seanperkins/ashleys-bed/output/media/ashleys-bed-closed.png

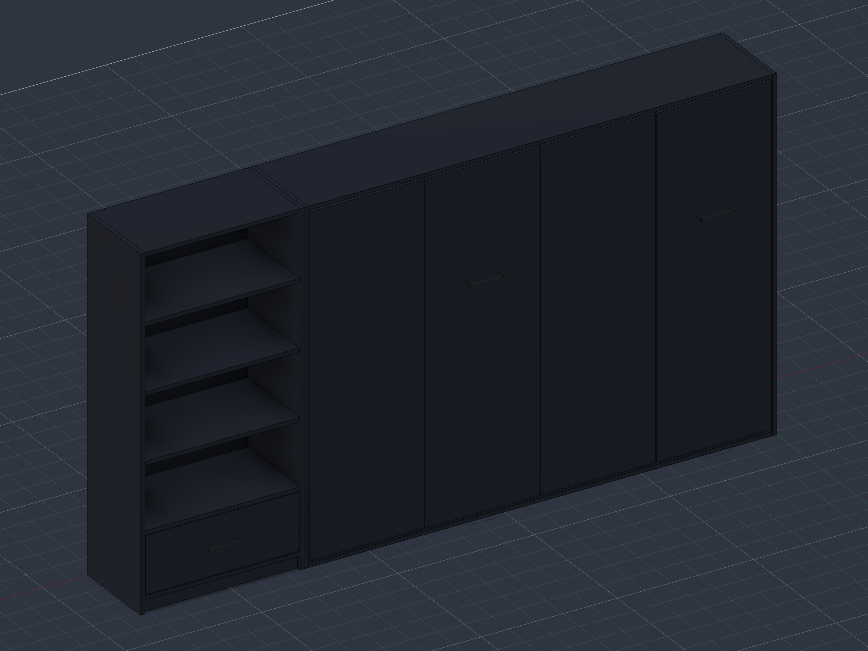
output/media/ashleys-bed-closed.png
