seanperkins/ashleys-bed/output/media/ashleys-bed-frame.png

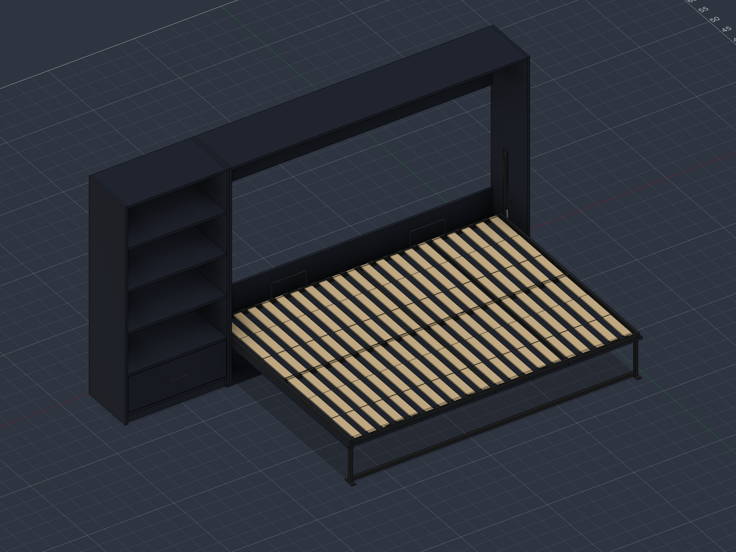
output/media/ashleys-bed-frame.png
