seanperkins/ashleys-bed/output/media/ashleys-bed-front.png

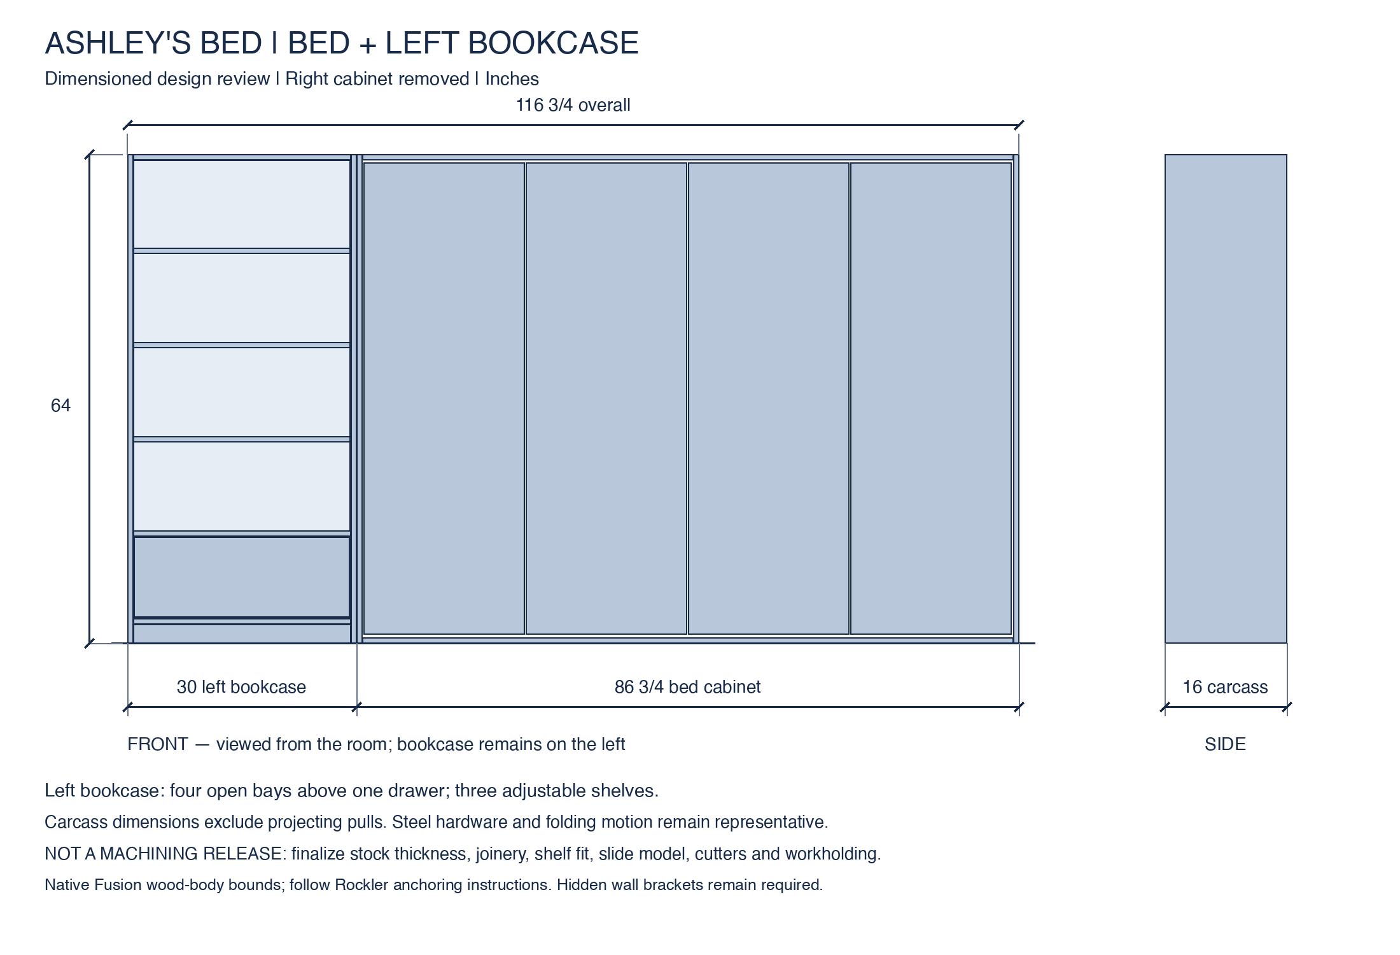
output/media/ashleys-bed-front.png
