seanperkins/ashleys-bed/output/media/ashleys-bed-open.png

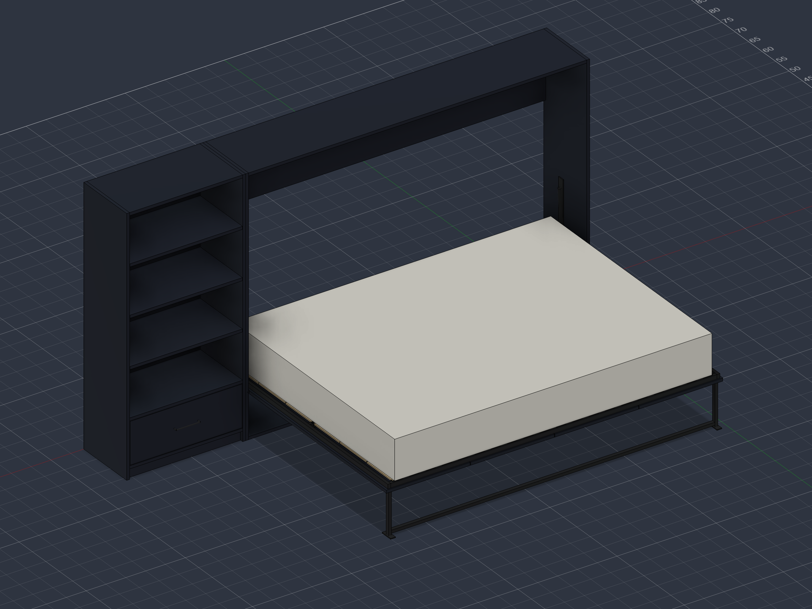
output/media/ashleys-bed-open.png
