seanperkins/ashleys-bed/output/media/ashleys-bed-overview.png

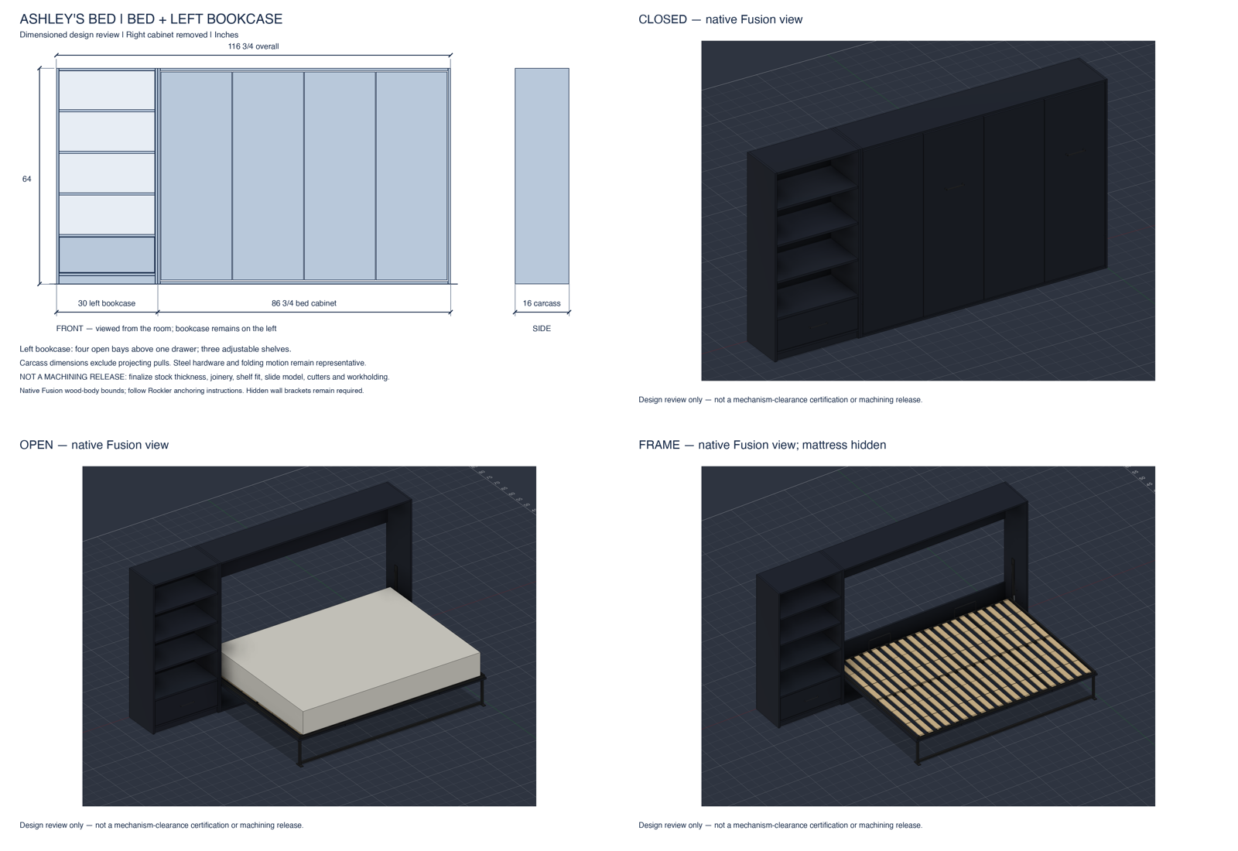
output/media/ashleys-bed-overview.png
