seanperkins/ashleys-bed/output/queen-horizontal-closed.png

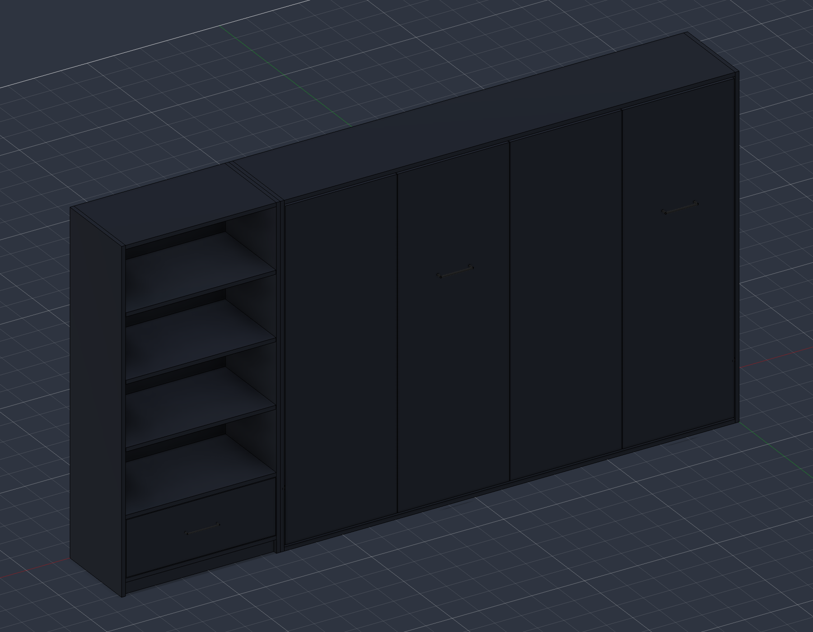
output/queen-horizontal-closed.png
