seanperkins/ashleys-bed/output/queen-horizontal-frame.png

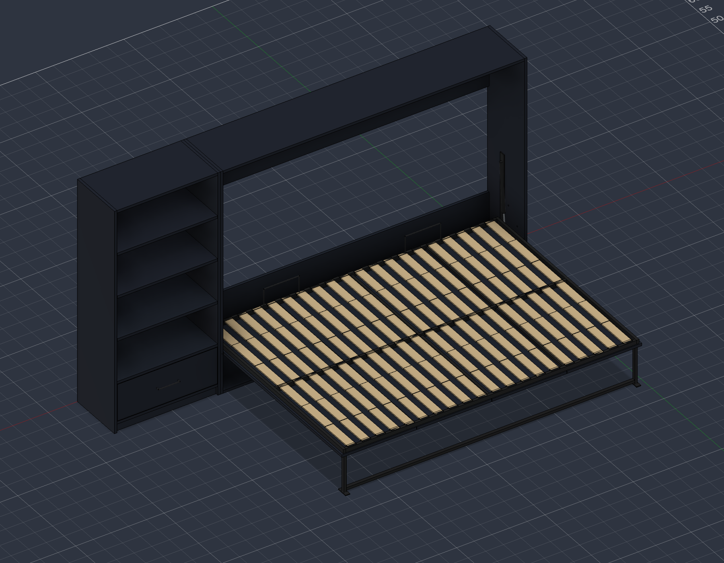
output/queen-horizontal-frame.png
