seanperkins/ashleys-bed/output/queen-horizontal-open.png

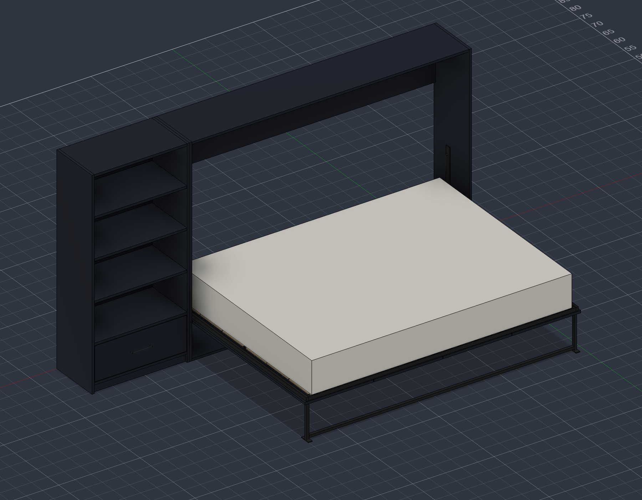
output/queen-horizontal-open.png
